GuruGuru-SEU/nrf-canon-remote/output/review/bottom-corner-locators.png

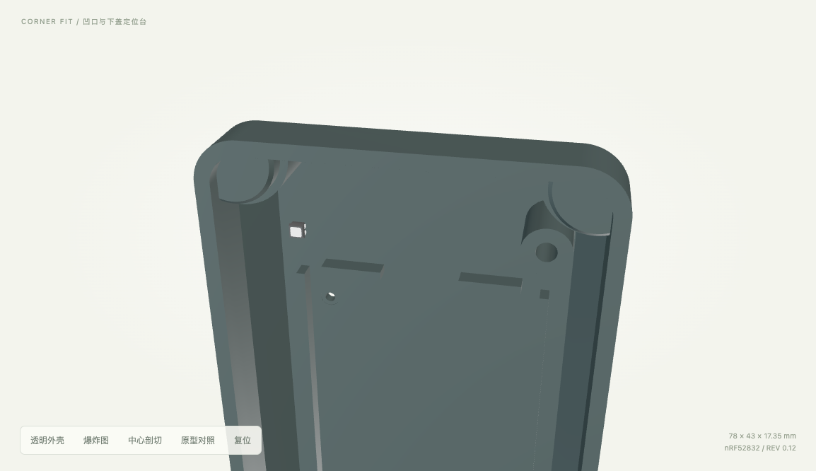
output/review/bottom-corner-locators.png
