GuruGuru-SEU/nrf-canon-remote/output/review/center-section.png

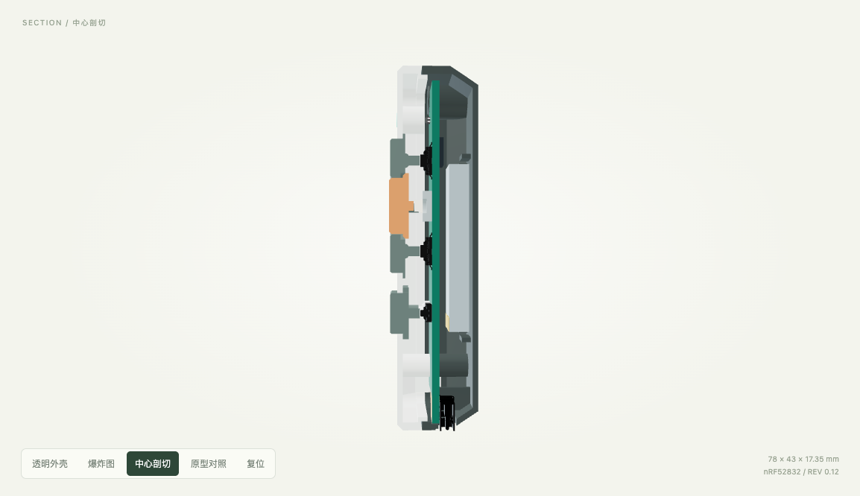
output/review/center-section.png
