GuruGuru-SEU/nrf-canon-remote/output/review/center-stage-1.png

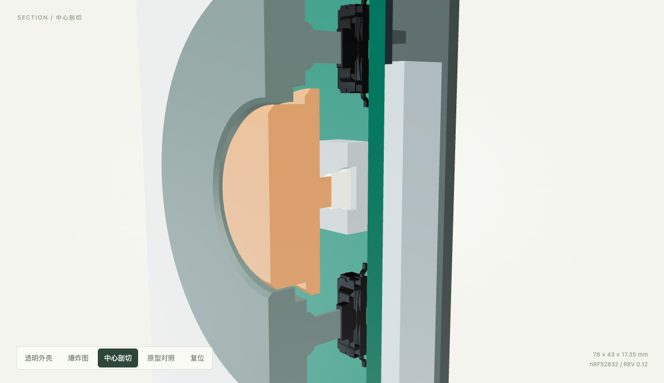
output/review/center-stage-1.png
