GuruGuru-SEU/nrf-canon-remote/output/review/center-switch-detail.png

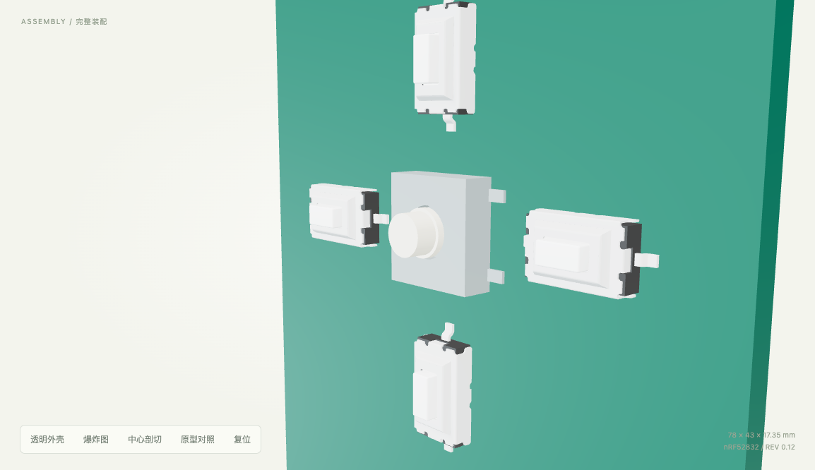
output/review/center-switch-detail.png
