GuruGuru-SEU/nrf-canon-remote/output/review/corner-fit.png

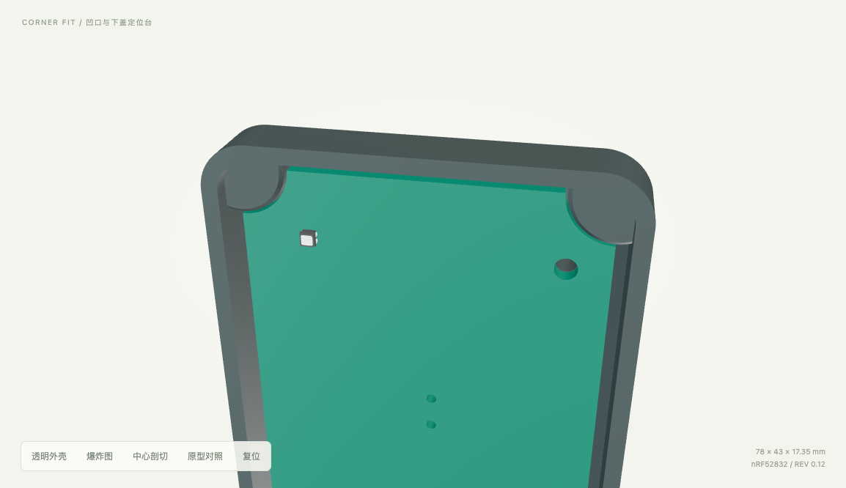
output/review/corner-fit.png
