GuruGuru-SEU/nrf-canon-remote/output/review/corner-notched-pcb.png

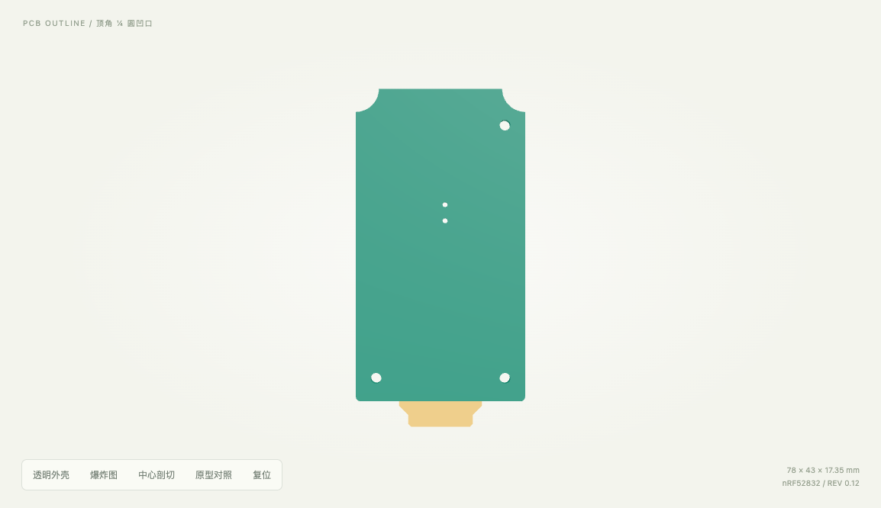
output/review/corner-notched-pcb.png
