GuruGuru-SEU/nrf-canon-remote/output/review/k2-1831sl-drawing.png

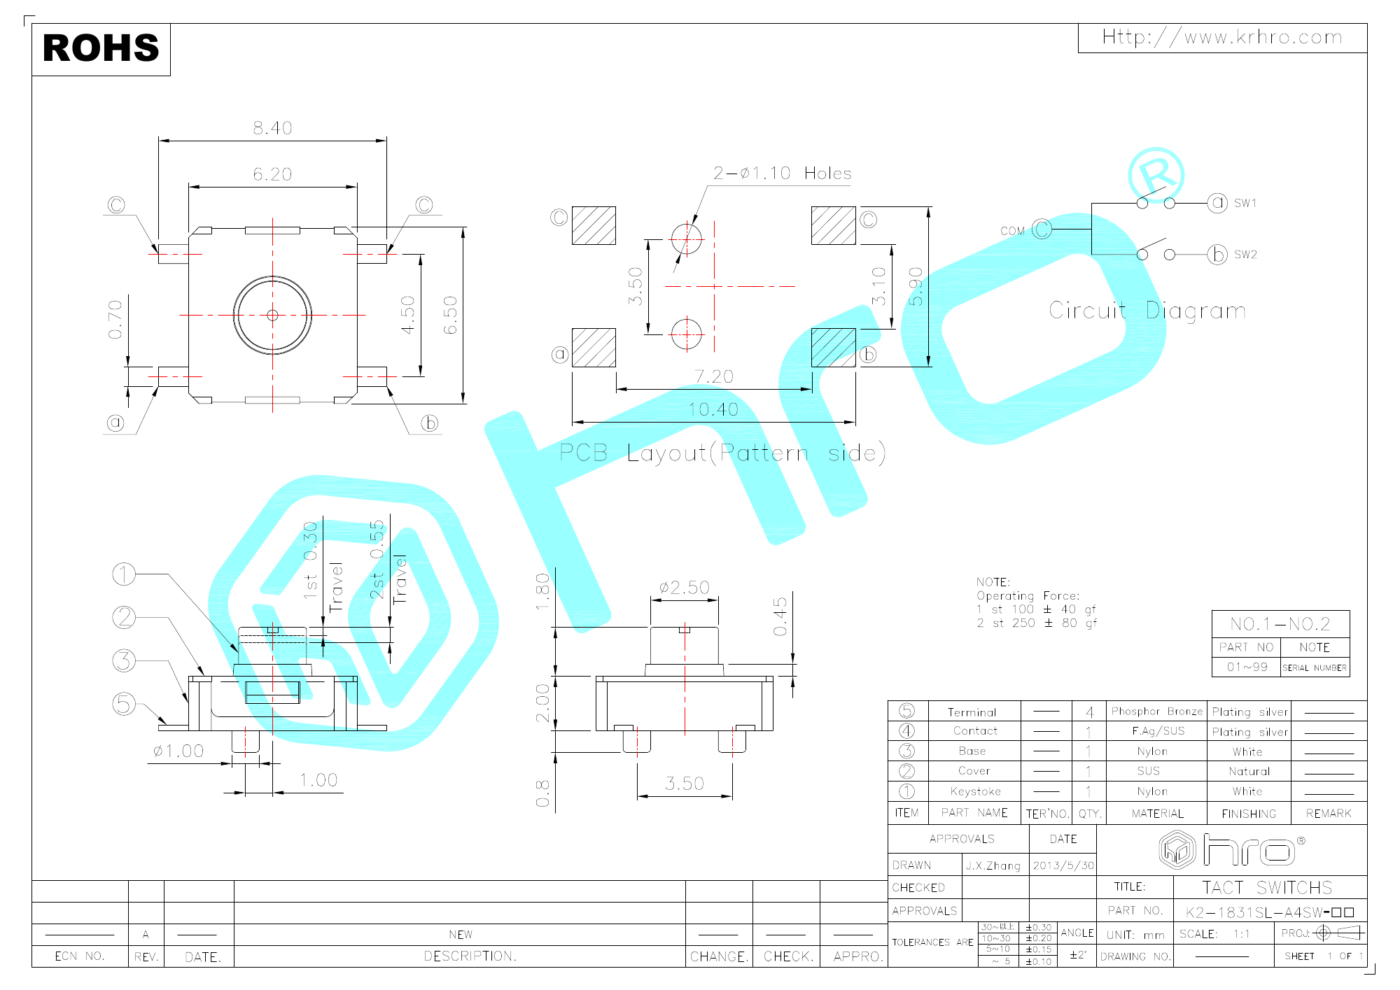
output/review/k2-1831sl-drawing.png
