GuruGuru-SEU/nrf-canon-remote/output/review/led-transparent.png

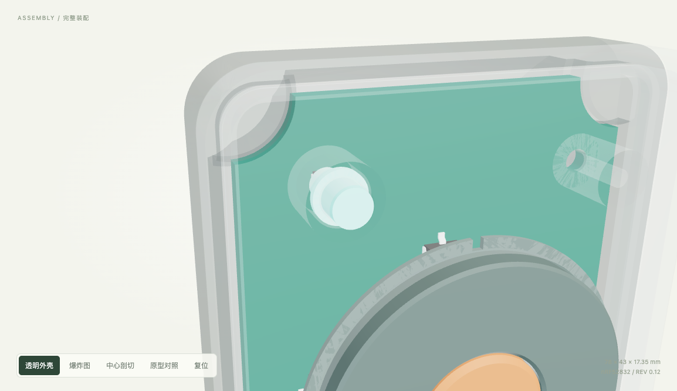
output/review/led-transparent.png
