GuruGuru-SEU/nrf-canon-remote/output/review/original-reference.png

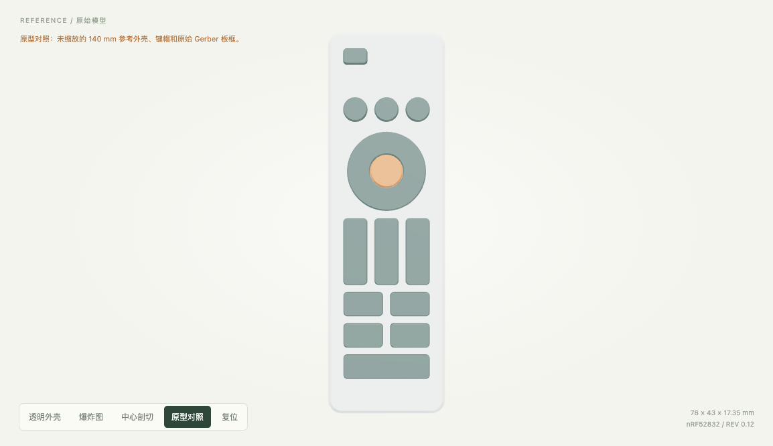
output/review/original-reference.png
