GuruGuru-SEU/nrf-canon-remote/output/review/preview-exploded.png

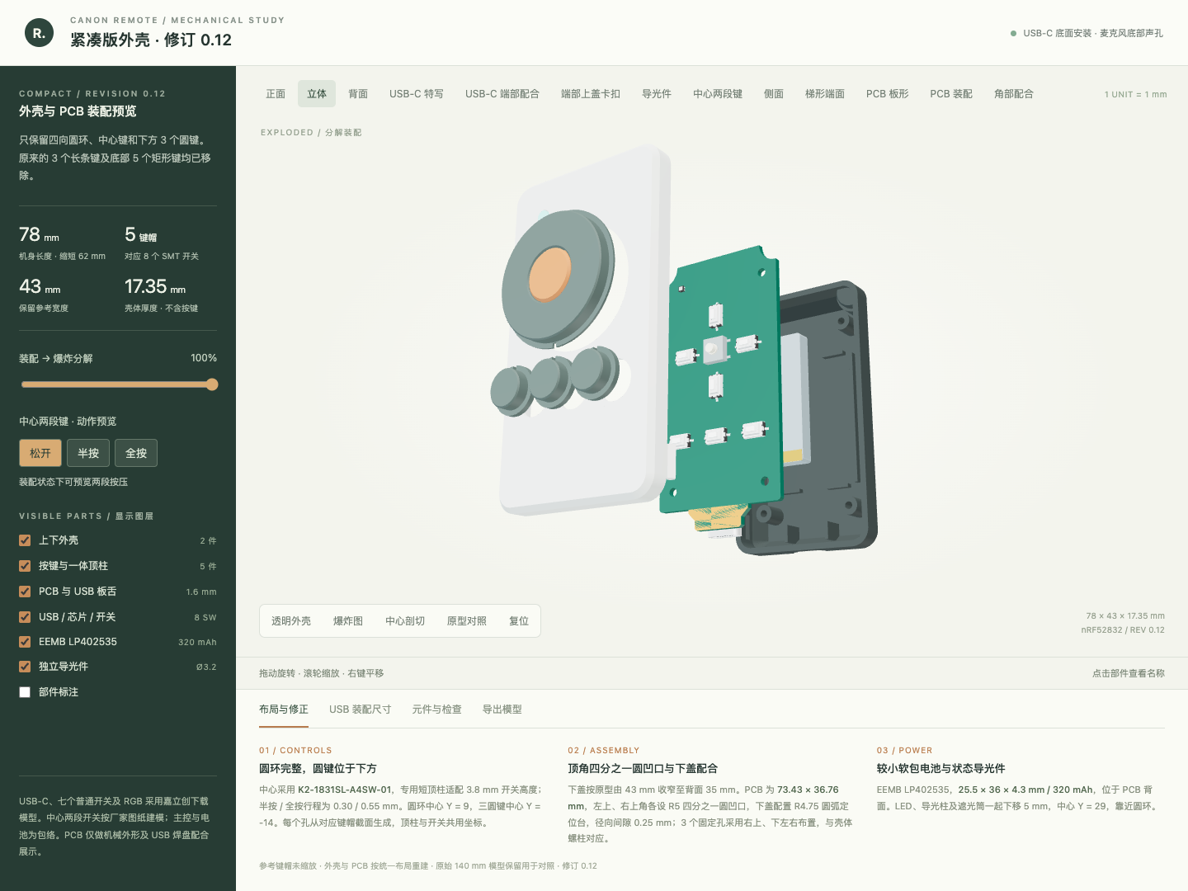
output/review/preview-exploded.png
