GuruGuru-SEU/nrf-canon-remote/output/review/preview-mobile.png

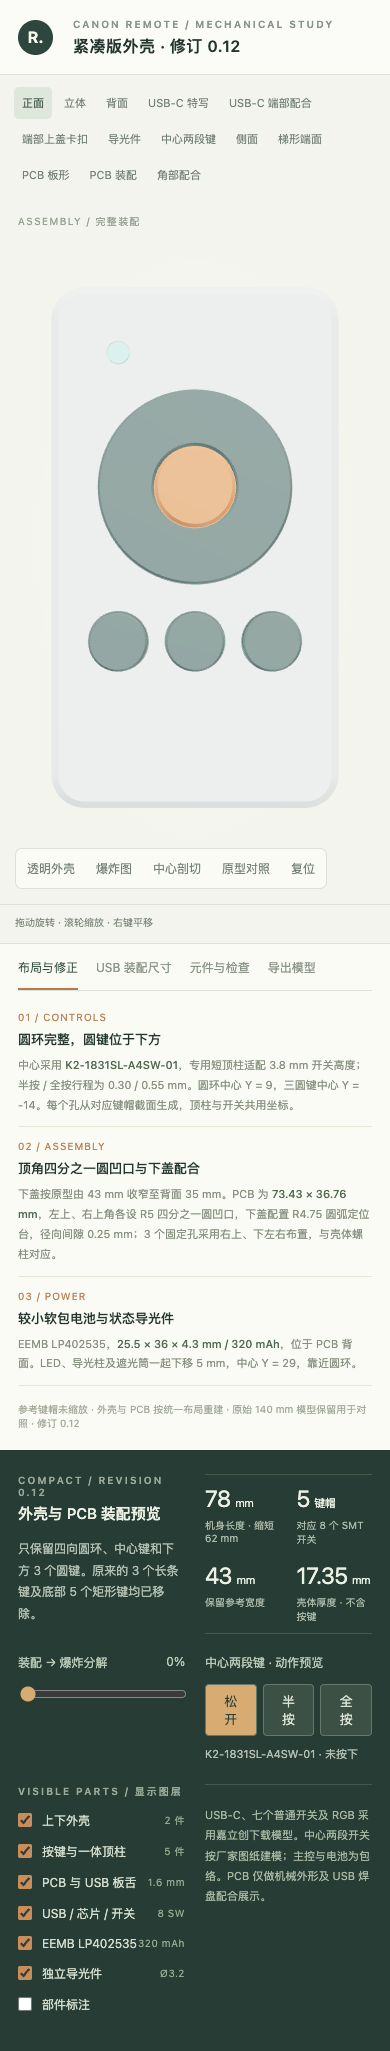
output/review/preview-mobile.png
