GuruGuru-SEU/nrf-canon-remote/output/review/preview-pcb.png

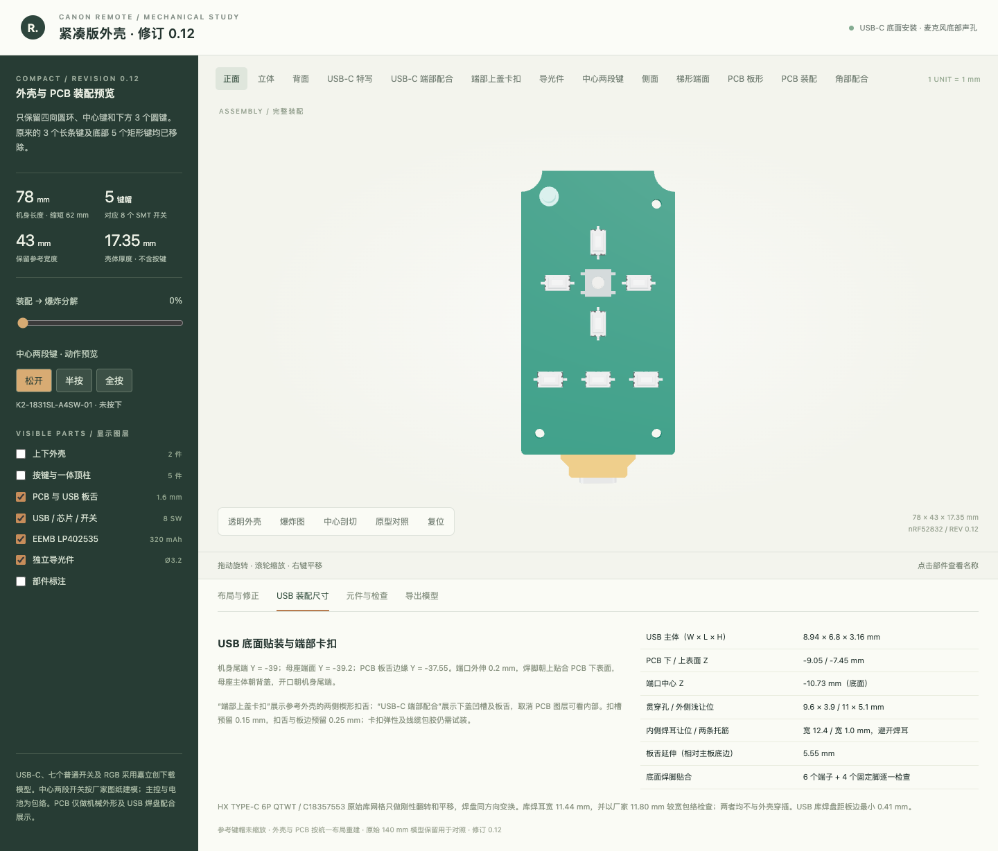
output/review/preview-pcb.png
