GuruGuru-SEU/nrf-canon-remote/output/review/preview-usb.png

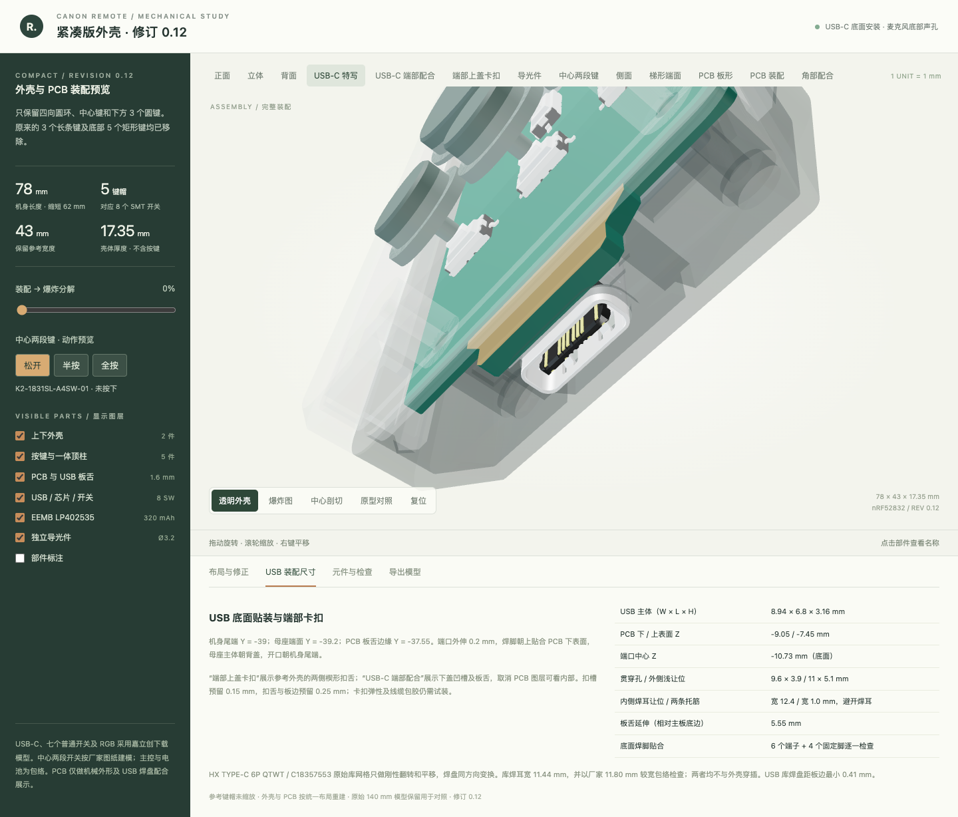
output/review/preview-usb.png
