GuruGuru-SEU/nrf-canon-remote/output/review/reference-pcb-retention.png

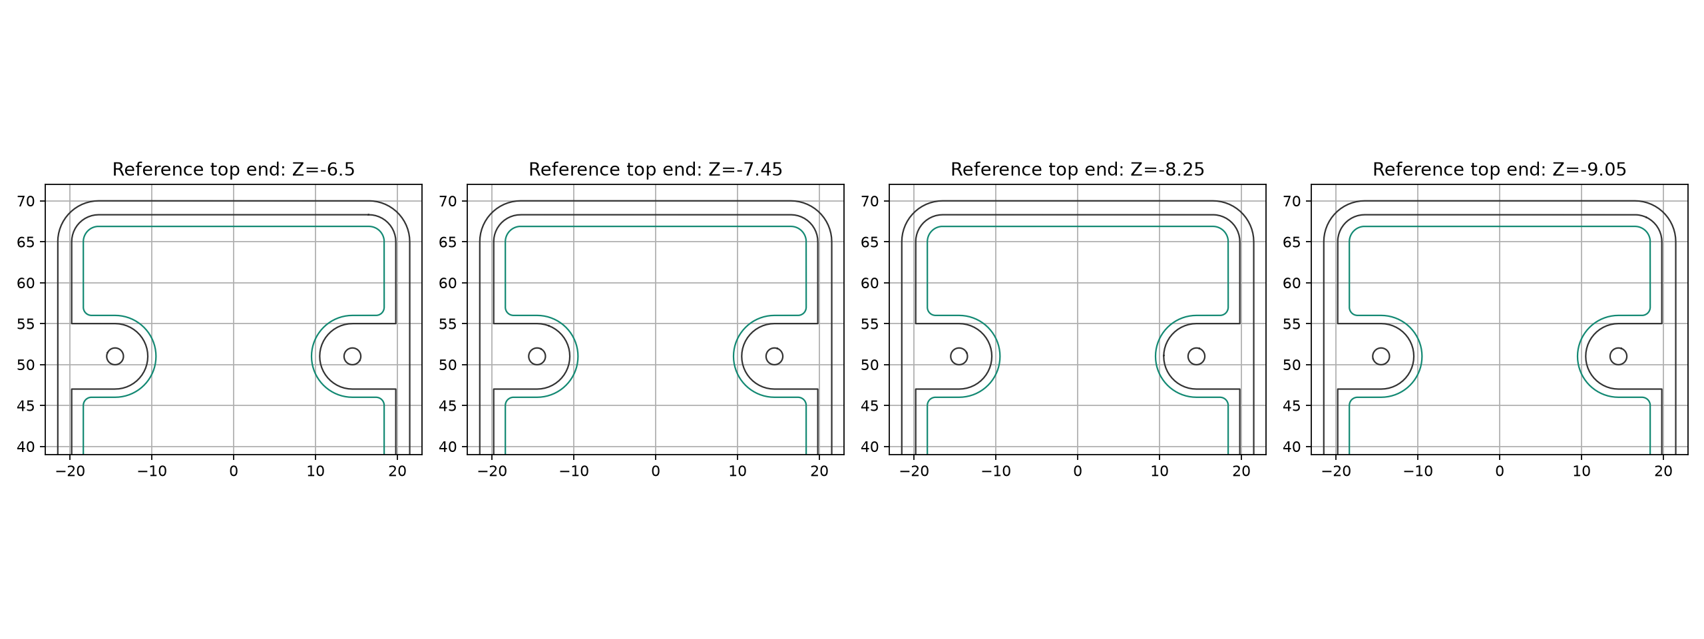
output/review/reference-pcb-retention.png
