GuruGuru-SEU/nrf-canon-remote/output/review/reference-sections.png

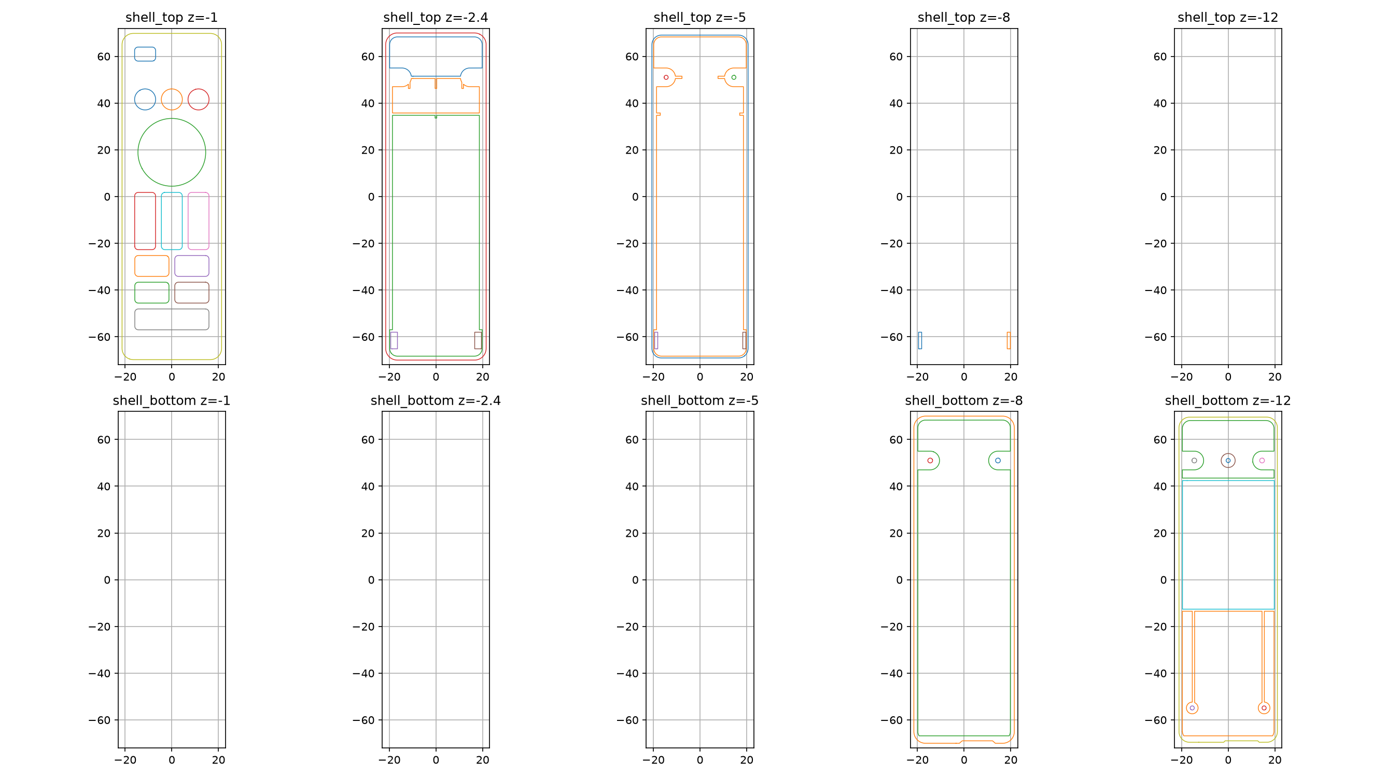
output/review/reference-sections.png
