GuruGuru-SEU/nrf-canon-remote/output/review/reference-trapezoid-end.png

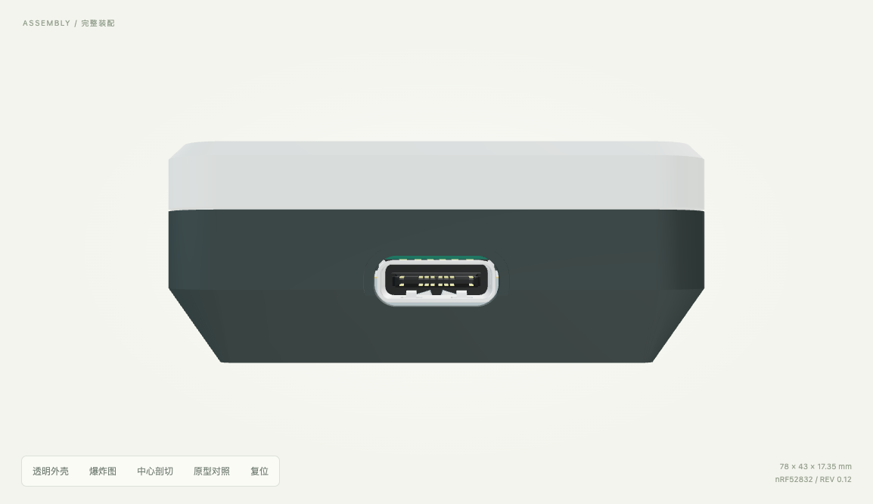
output/review/reference-trapezoid-end.png
