GuruGuru-SEU/nrf-canon-remote/output/review/reference-usb-sections.png

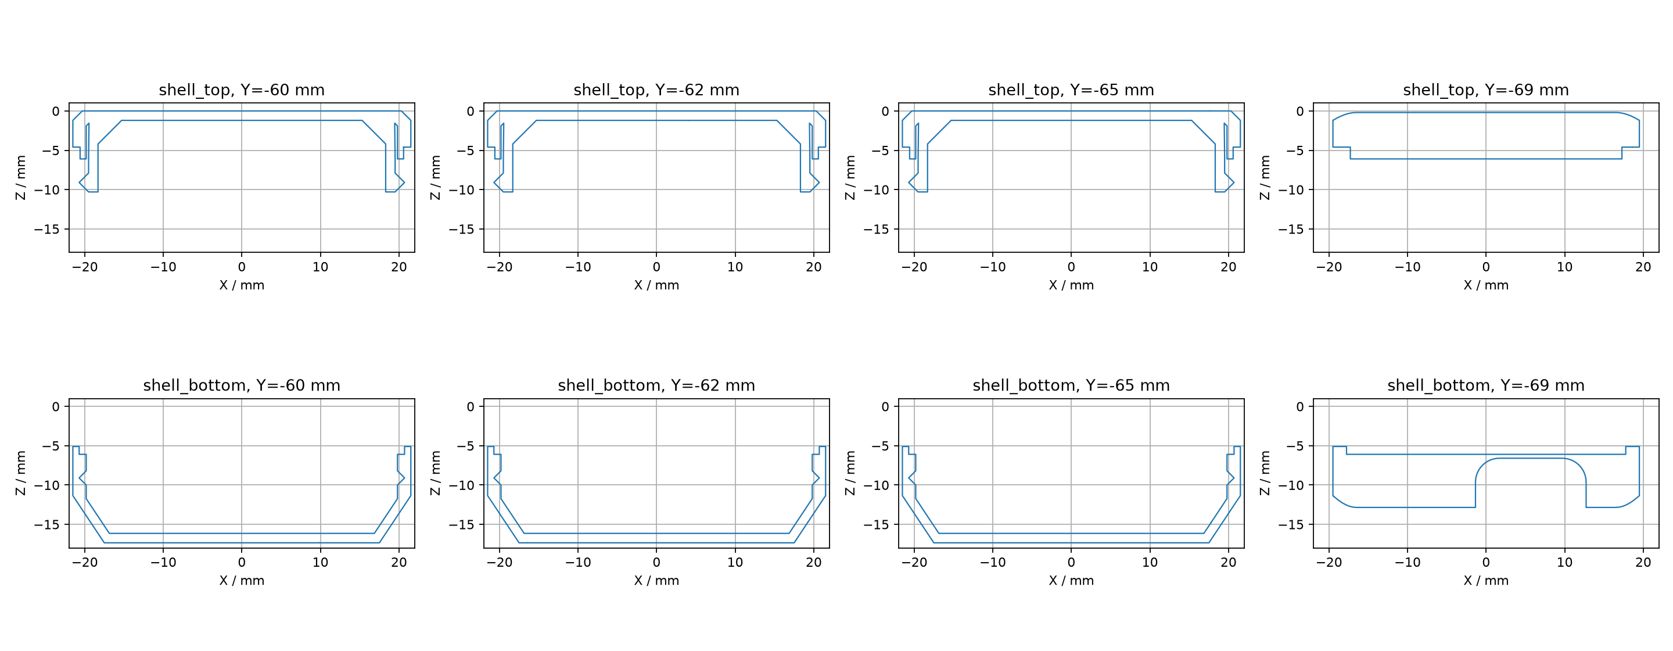
output/review/reference-usb-sections.png
