GuruGuru-SEU/nrf-canon-remote/output/review/reference-usb-structures.png

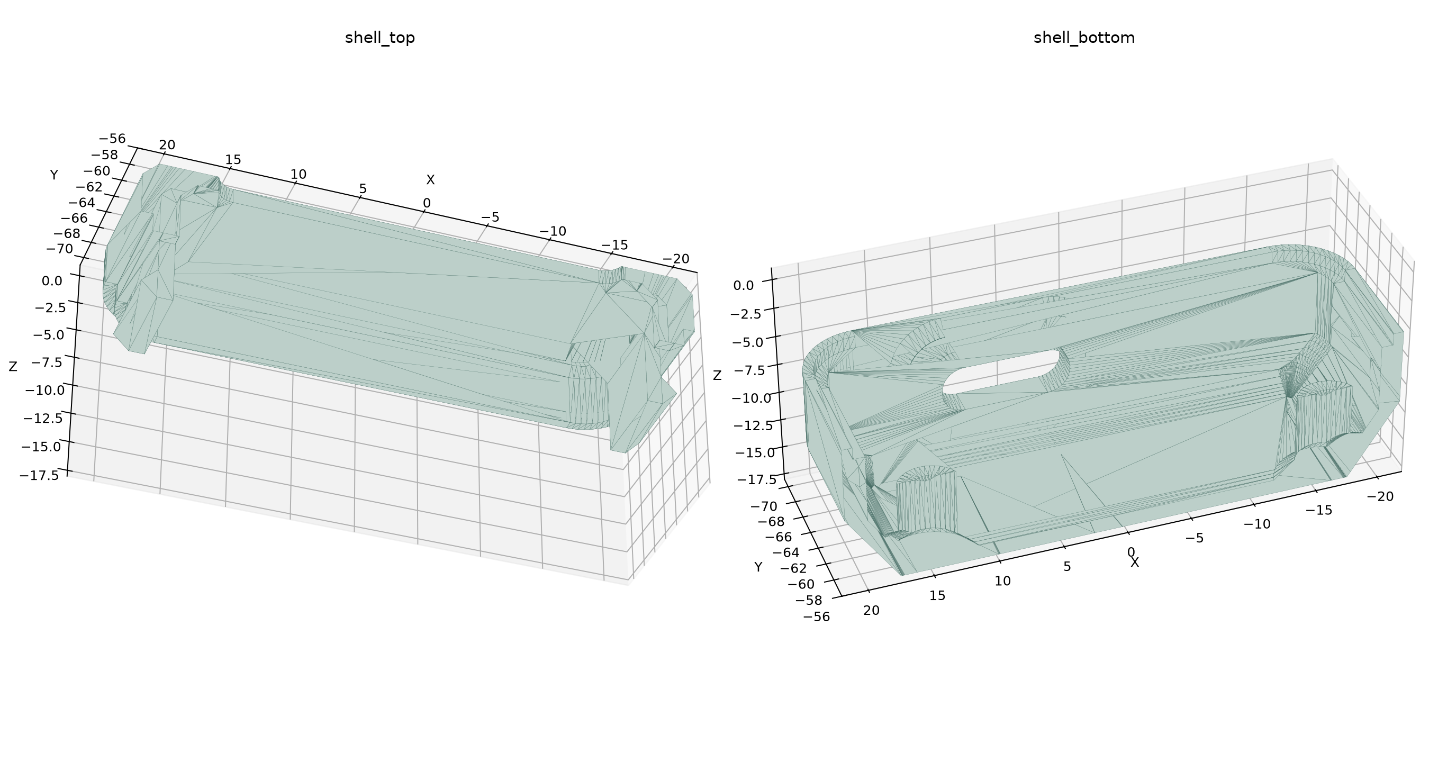
output/review/reference-usb-structures.png
