GuruGuru-SEU/nrf-canon-remote/output/review/reference-xz-profile.png

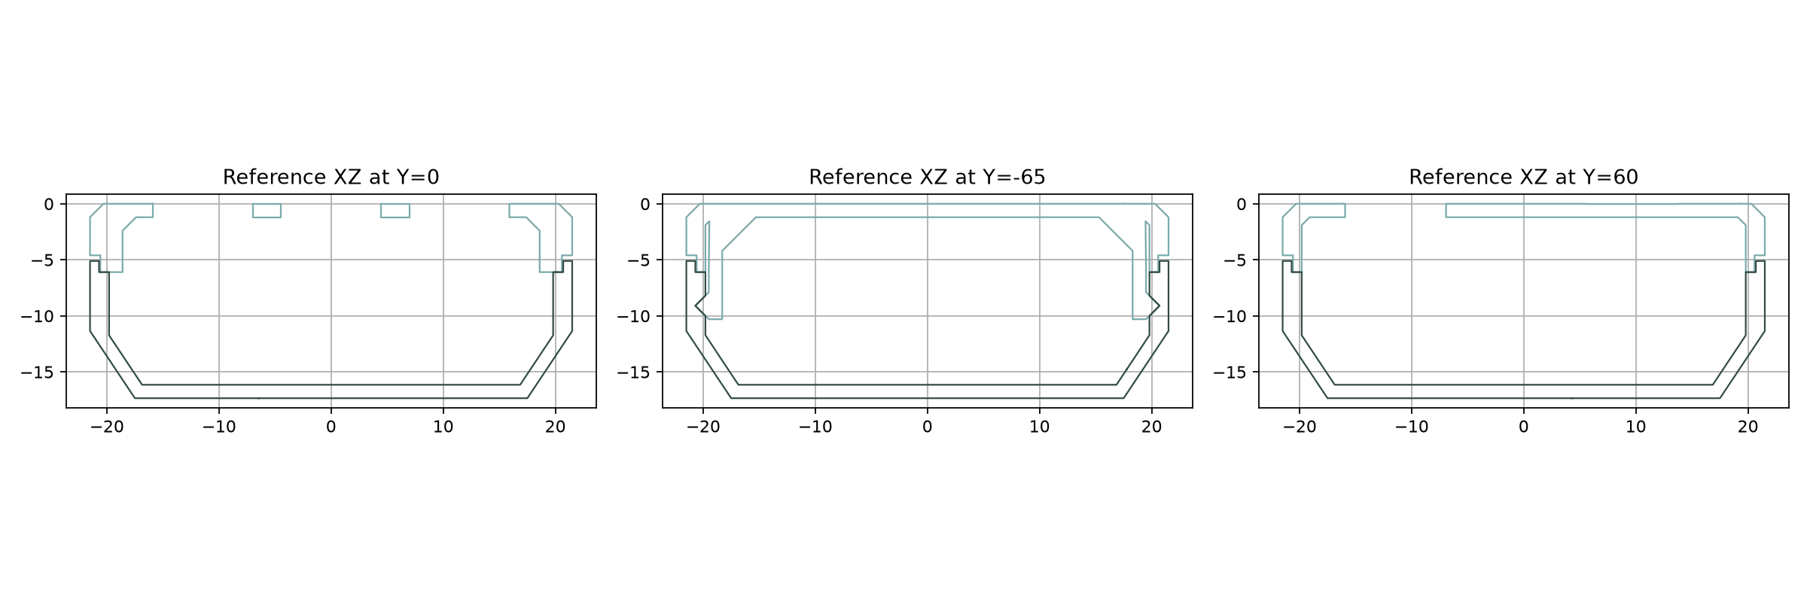
output/review/reference-xz-profile.png
