GuruGuru-SEU/nrf-canon-remote/output/review/switch-drawing.png

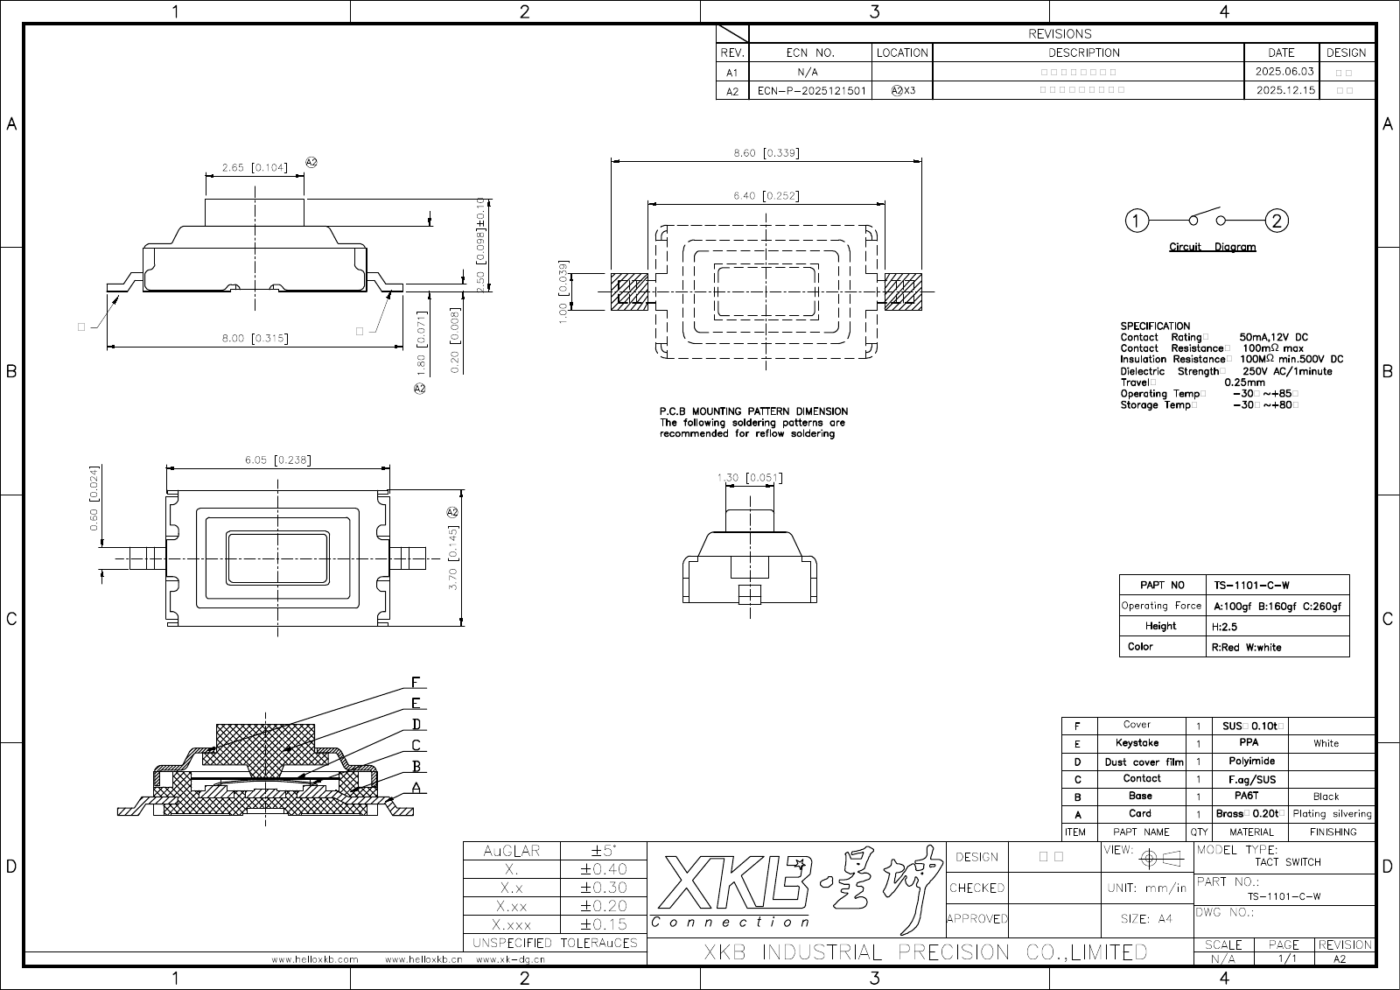
output/review/switch-drawing.png
