GuruGuru-SEU/nrf-canon-remote/output/review/transverse.png

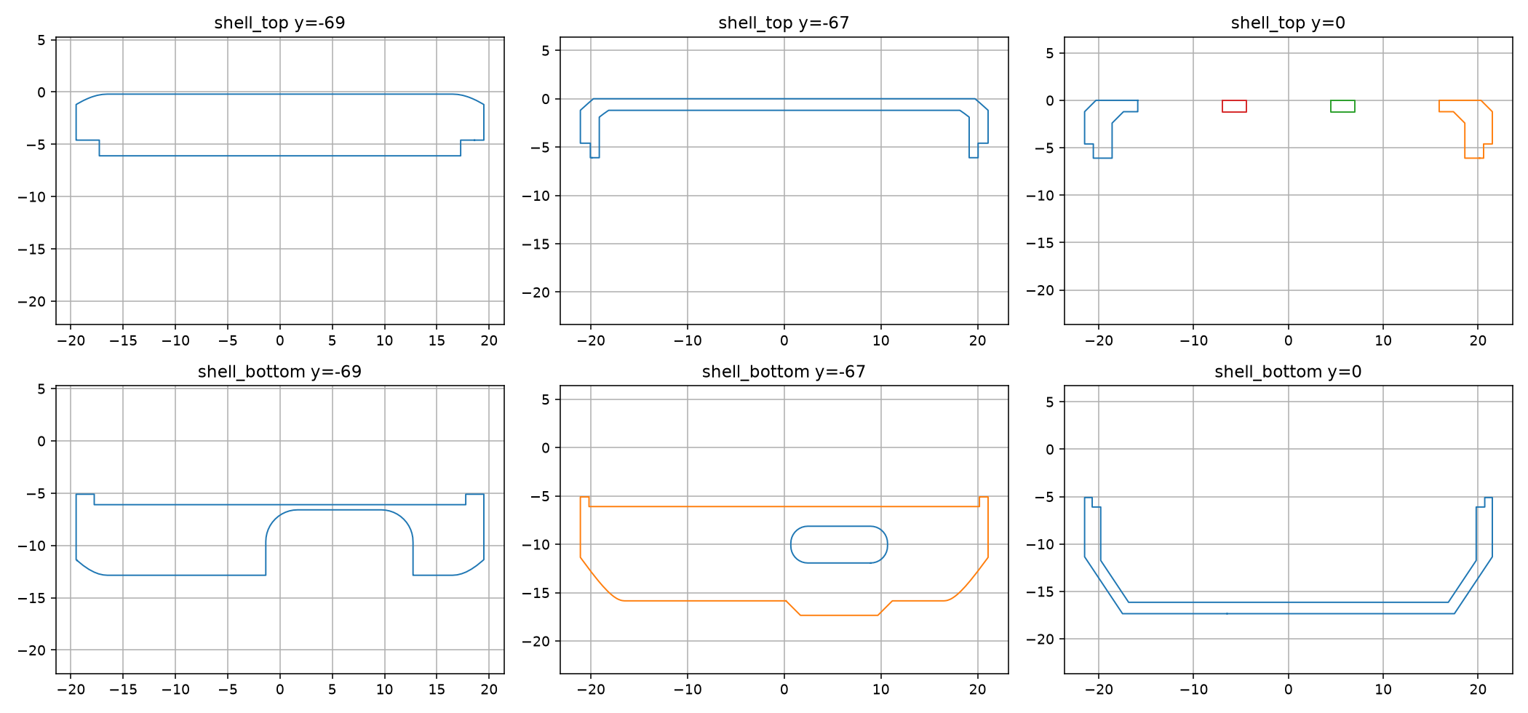
output/review/transverse.png
