GuruGuru-SEU/nrf-canon-remote/output/review/usb-drawing.png

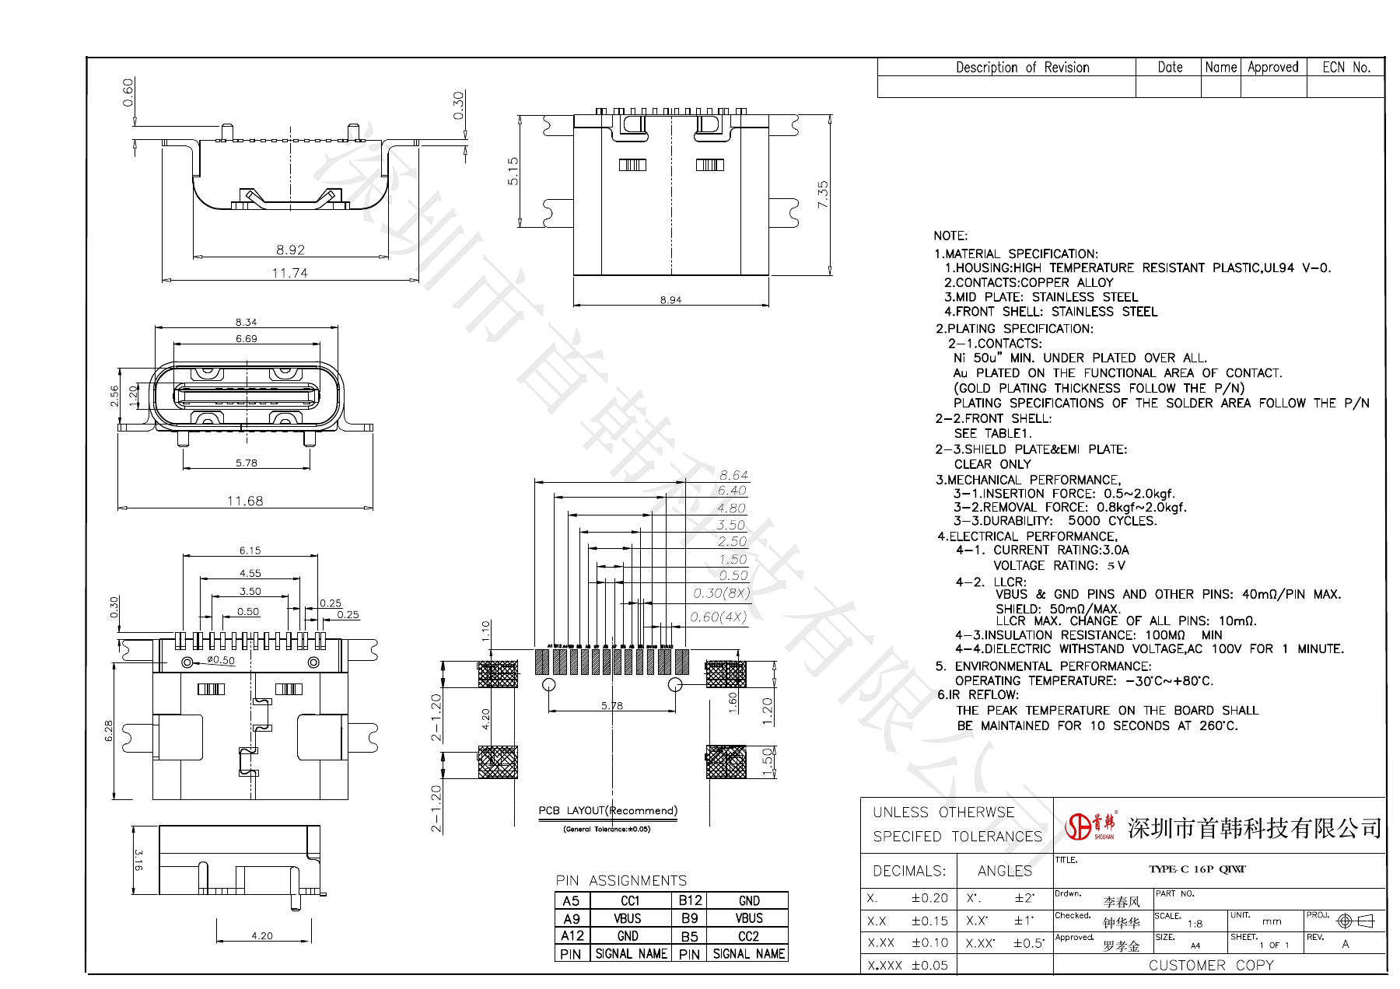
output/review/usb-drawing.png
