GuruGuru-SEU/nrf-canon-remote/output/review/usb-end-fit.png

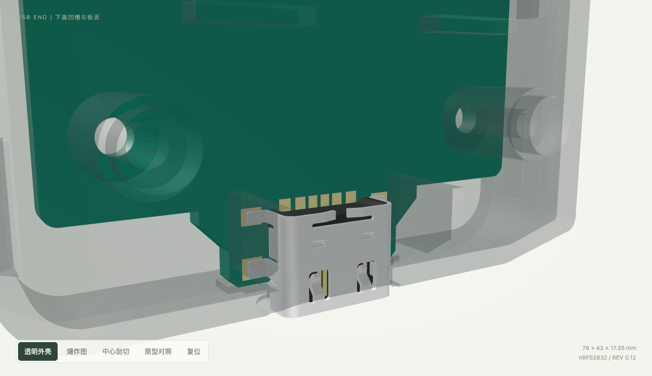
output/review/usb-end-fit.png
