GuruGuru-SEU/nrf-canon-remote/output/review/usb-end-sockets.png

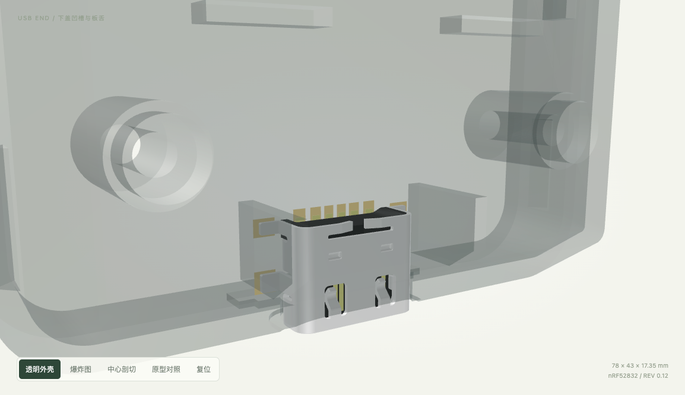
output/review/usb-end-sockets.png
