GuruGuru-SEU/nrf-canon-remote/output/review/usb-end-top-latches.png

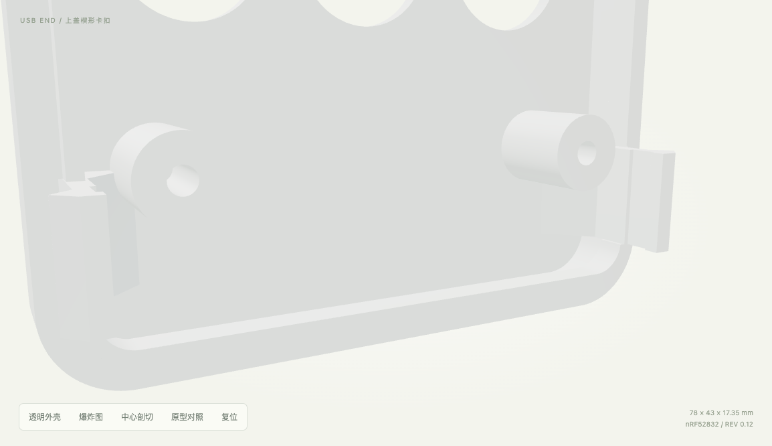
output/review/usb-end-top-latches.png
