GuruGuru-SEU/nrf-canon-remote/output/review/usb-fit-sections.png

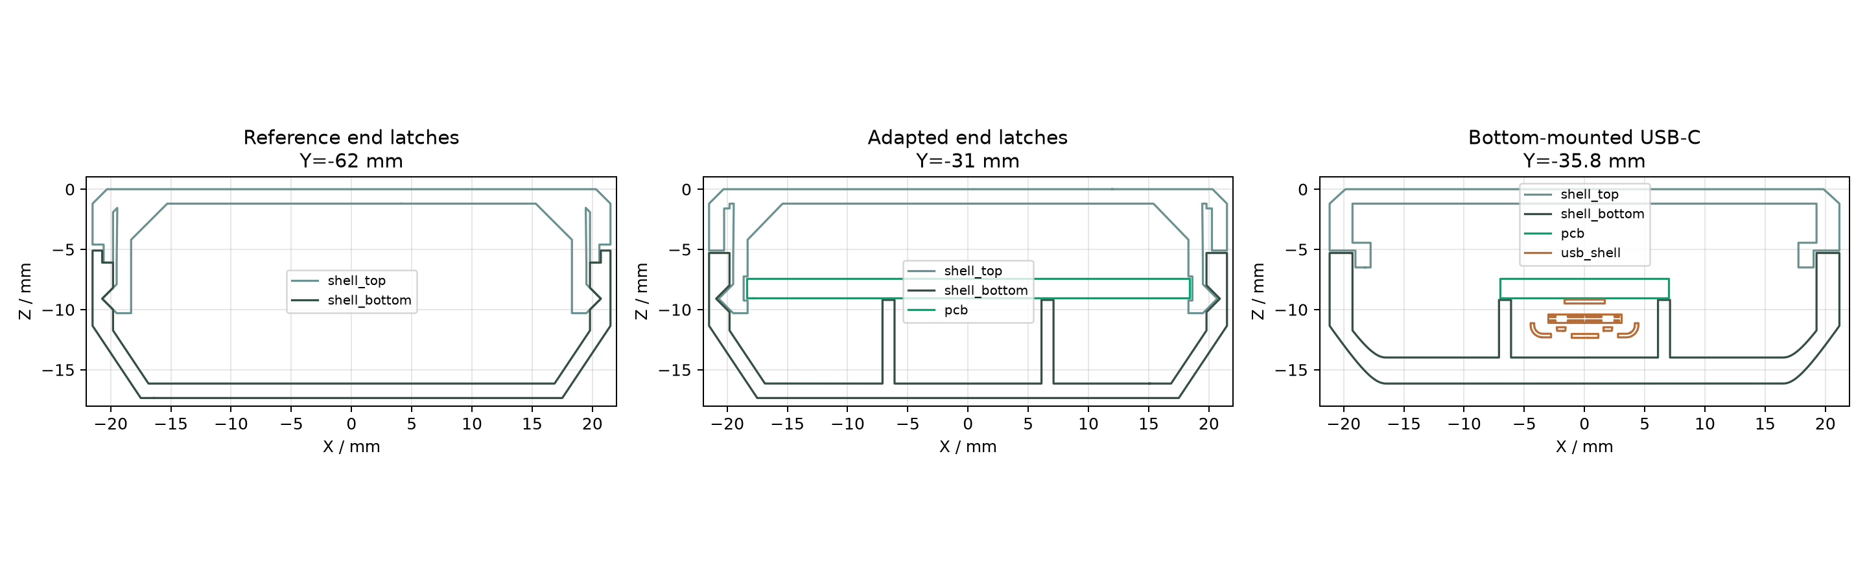
output/review/usb-fit-sections.png
