GuruGuru-SEU/nrf-canon-remote/output/review/usb-opaque.png

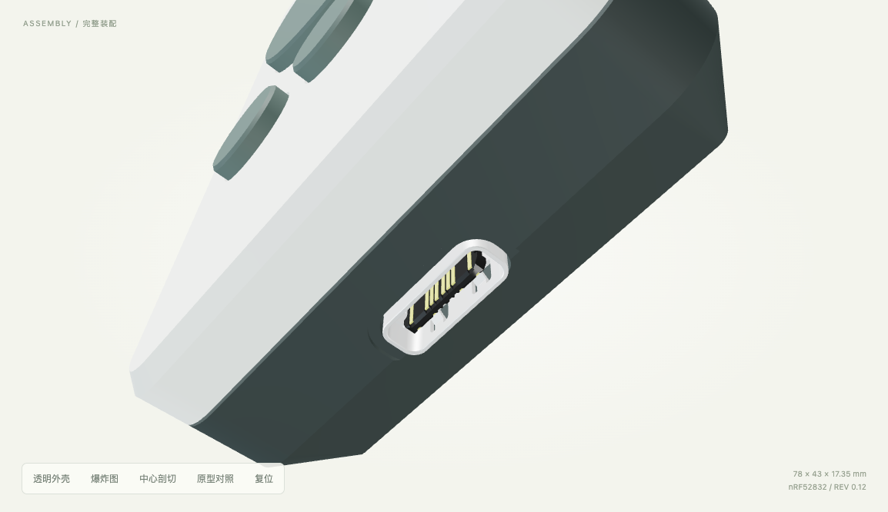
output/review/usb-opaque.png
