GuruGuru-SEU/nrf-canon-remote/output/rf/comparison.png

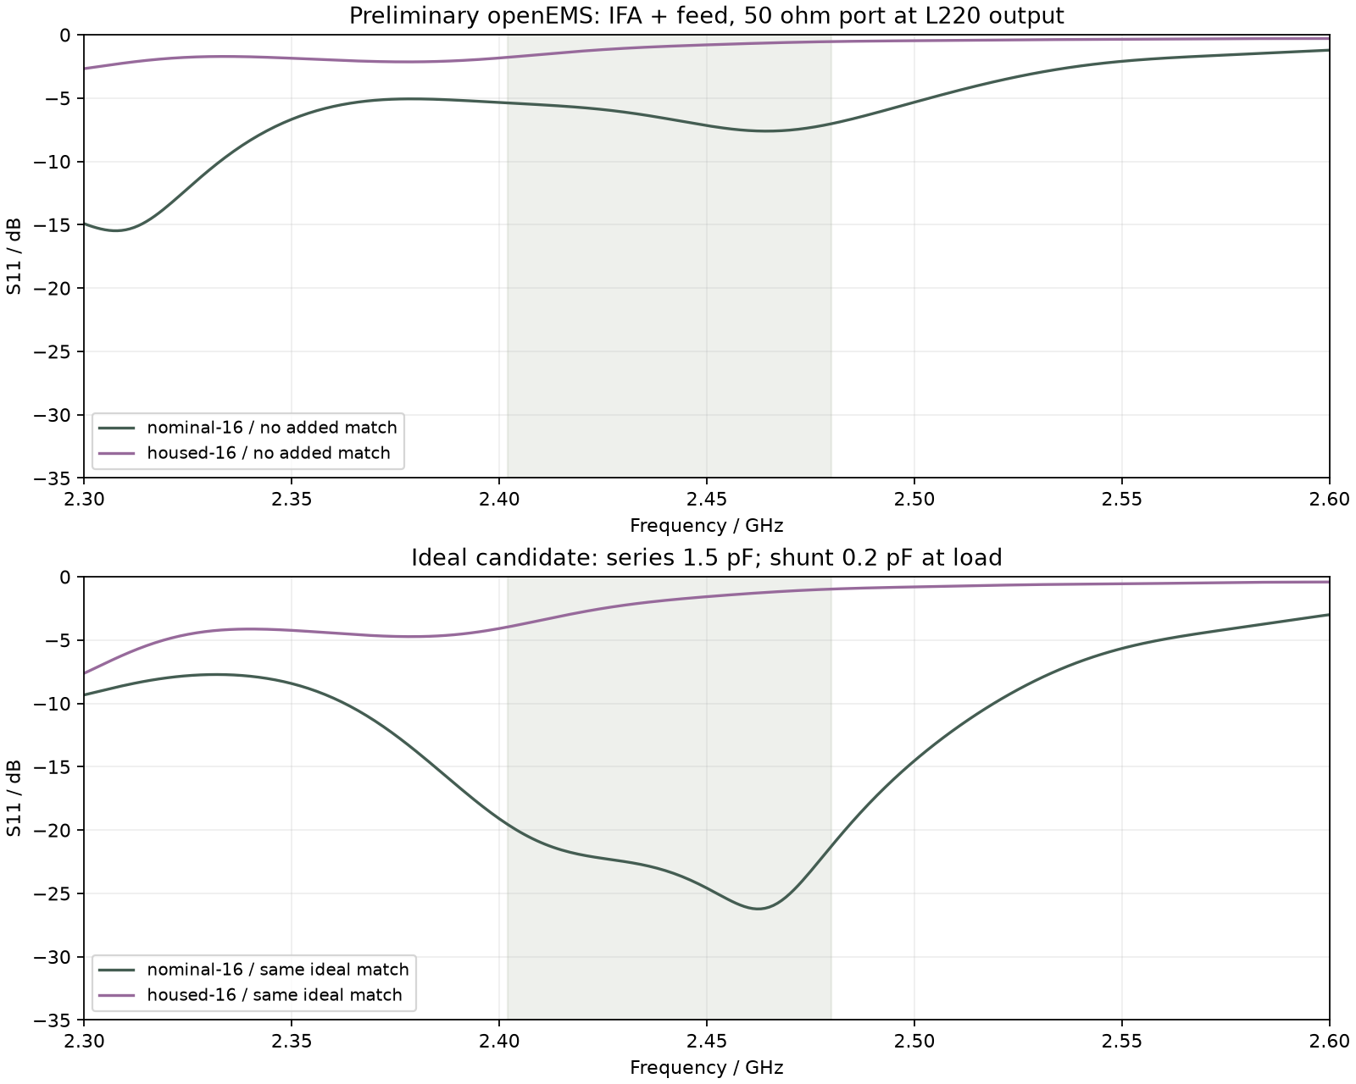
output/rf/comparison.png
