GuruGuru-SEU/nrf-canon-remote/output/rf/geometry.png

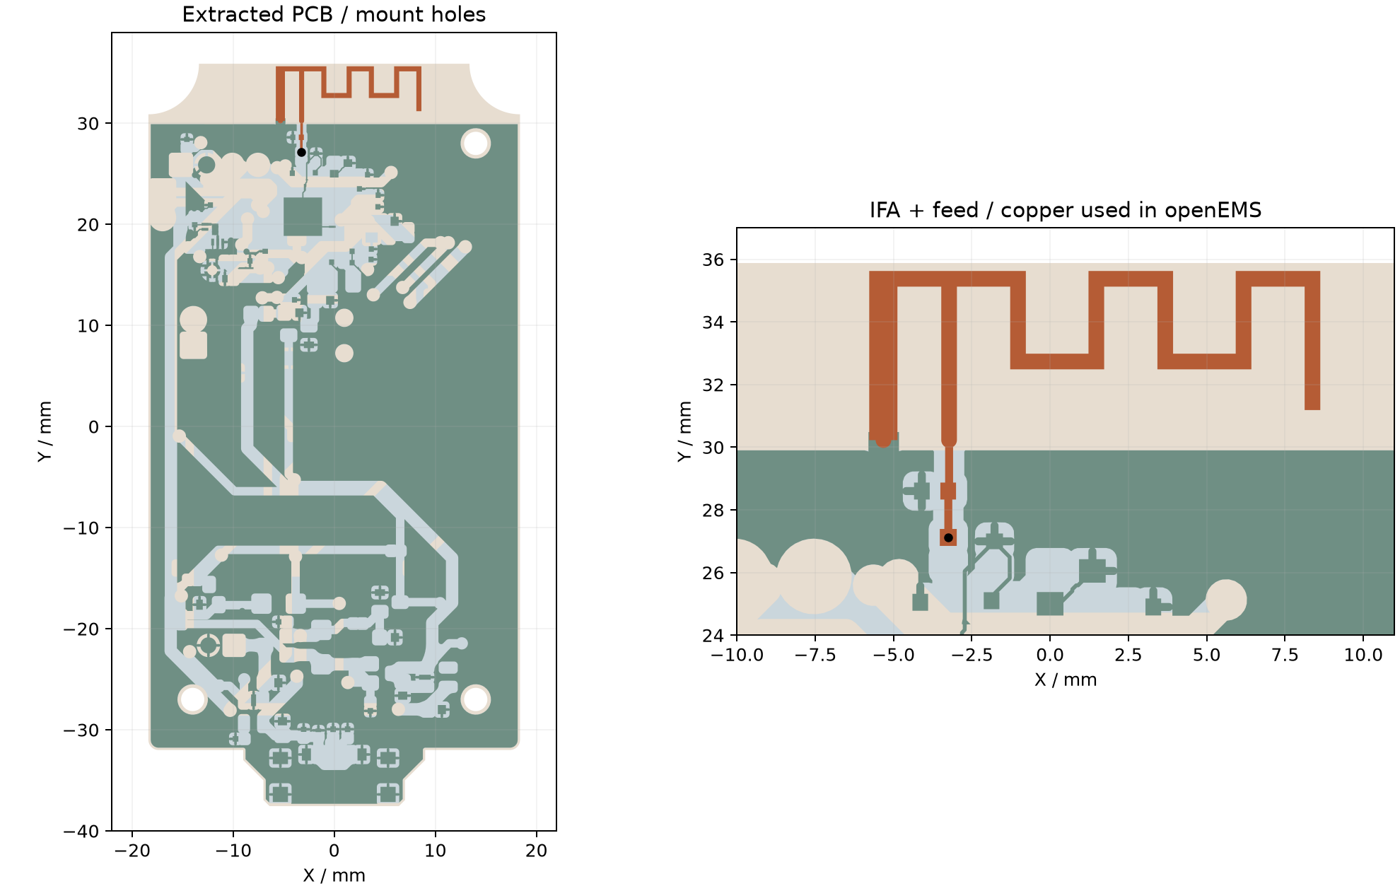
output/rf/geometry.png
