GuruGuru-SEU/nrf-canon-remote/output/rf/housed-comparison.png

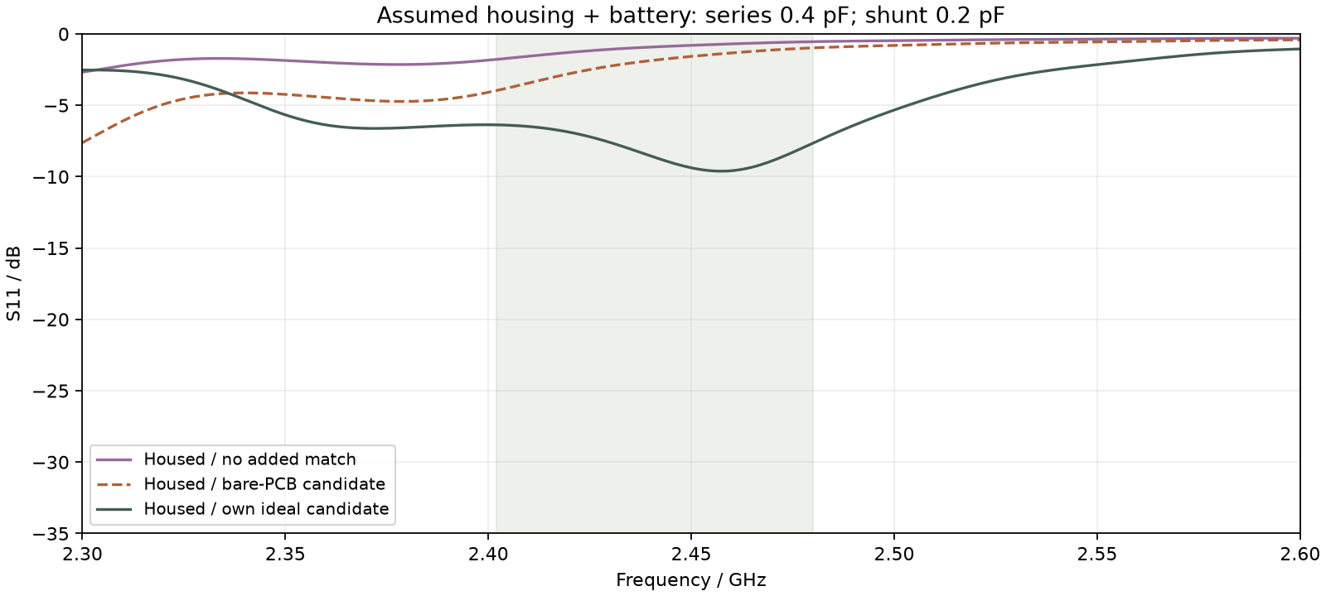
output/rf/housed-comparison.png
