GuruGuru-SEU/nrf-canon-remote/output/review/materials-checks.png

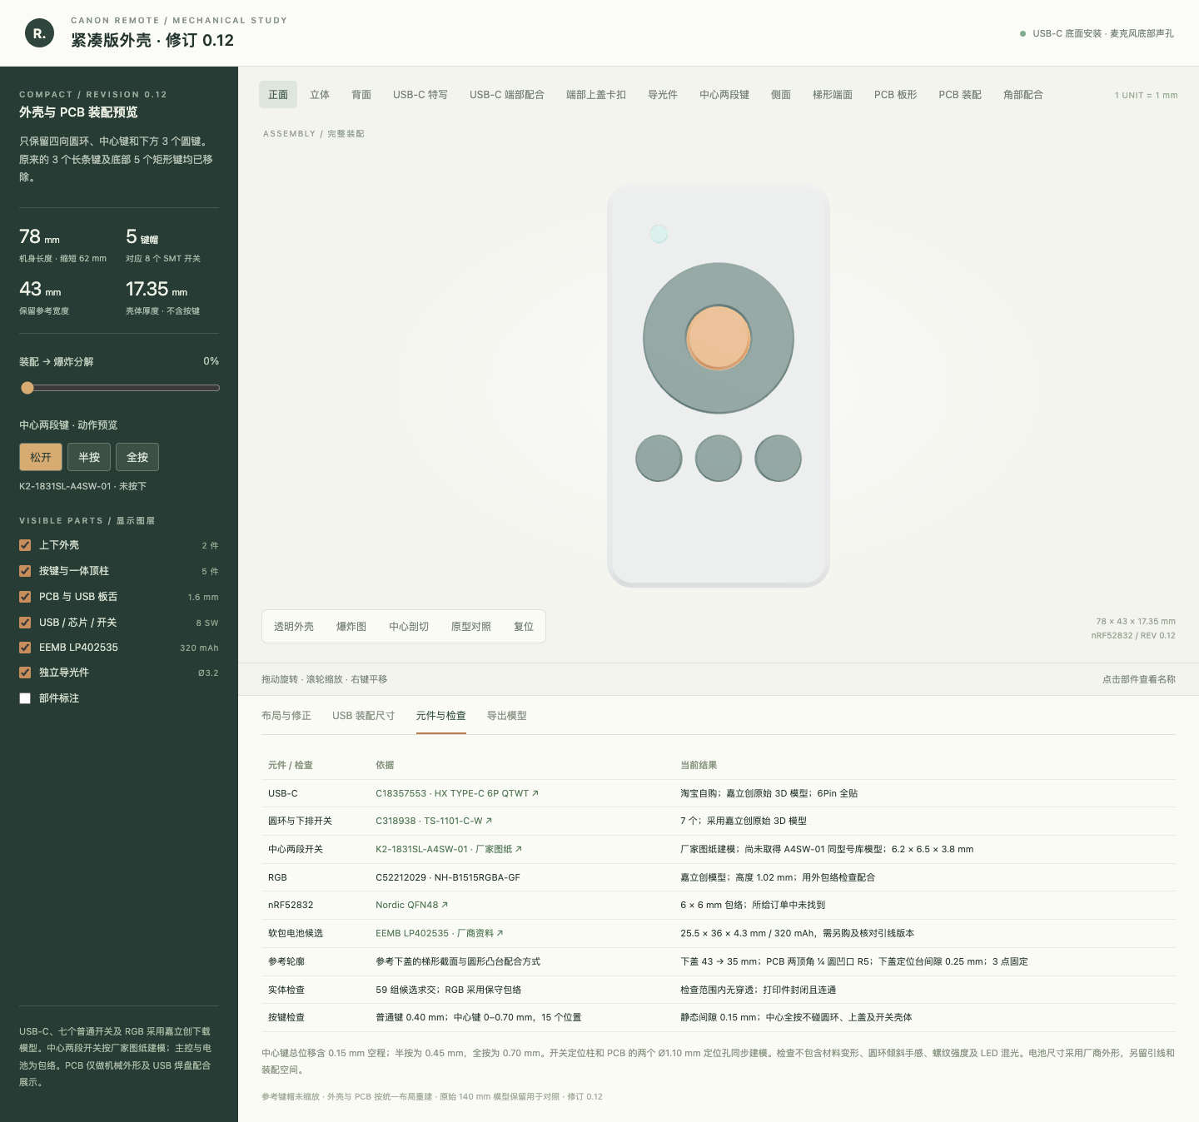
output/review/materials-checks.png
