GuruGuru-SEU/nrf-canon-remote/reference/component-models/C318938.obj

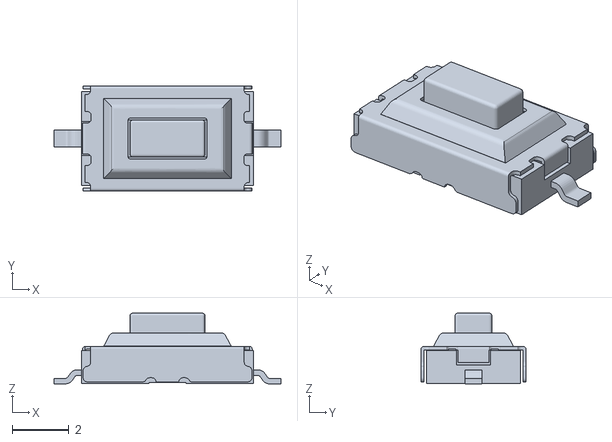
[picture p49: CAD file, 2026-09-16]
reference/component-models/C318938.obj
8.01 x 3.70 x 2.50
