GuruGuru-SEU/nrf-canon-remote/output/review/assembly-isometric.png

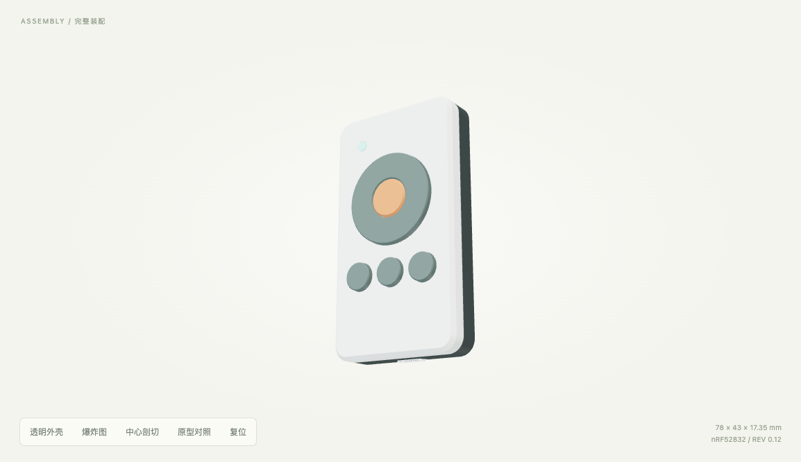
output/review/assembly-isometric.png
