GuruGuru-SEU/nrf-canon-remote/output/review/preview-assembled.png

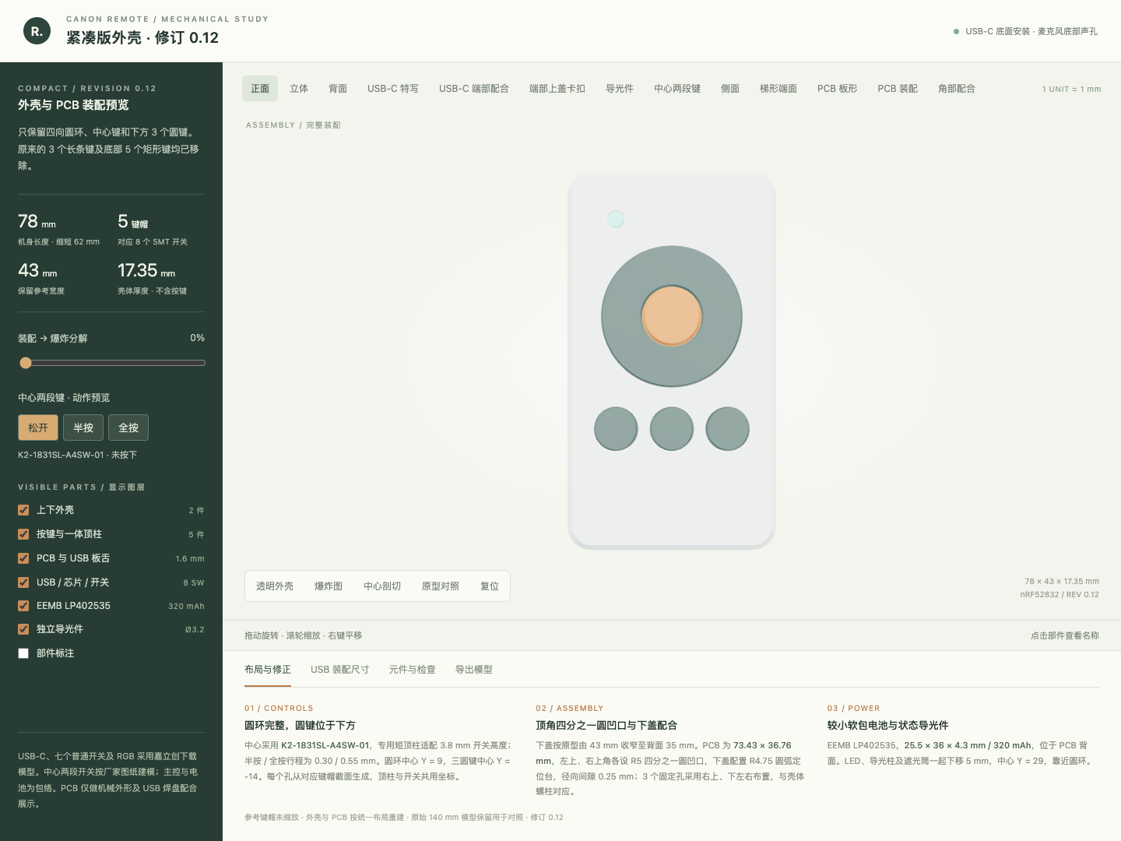
output/review/preview-assembled.png
