GuruGuru-SEU/nrf-canon-remote/output/review/usb-solder-face.png

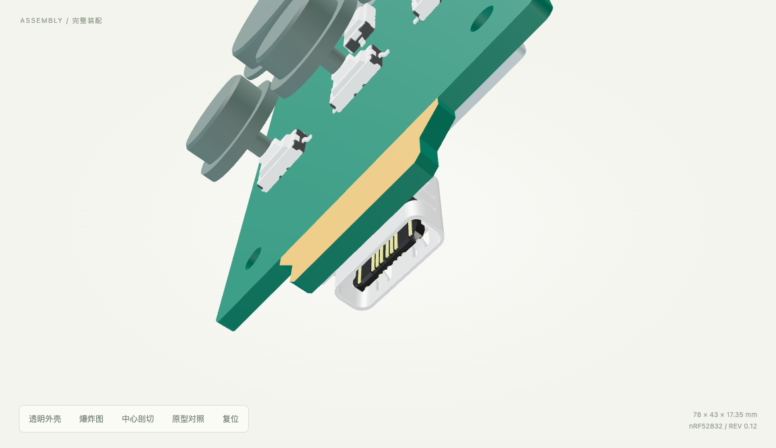
output/review/usb-solder-face.png
